paschendale1917/motocounter/photo_2025-11-30_00-51-59.jpg

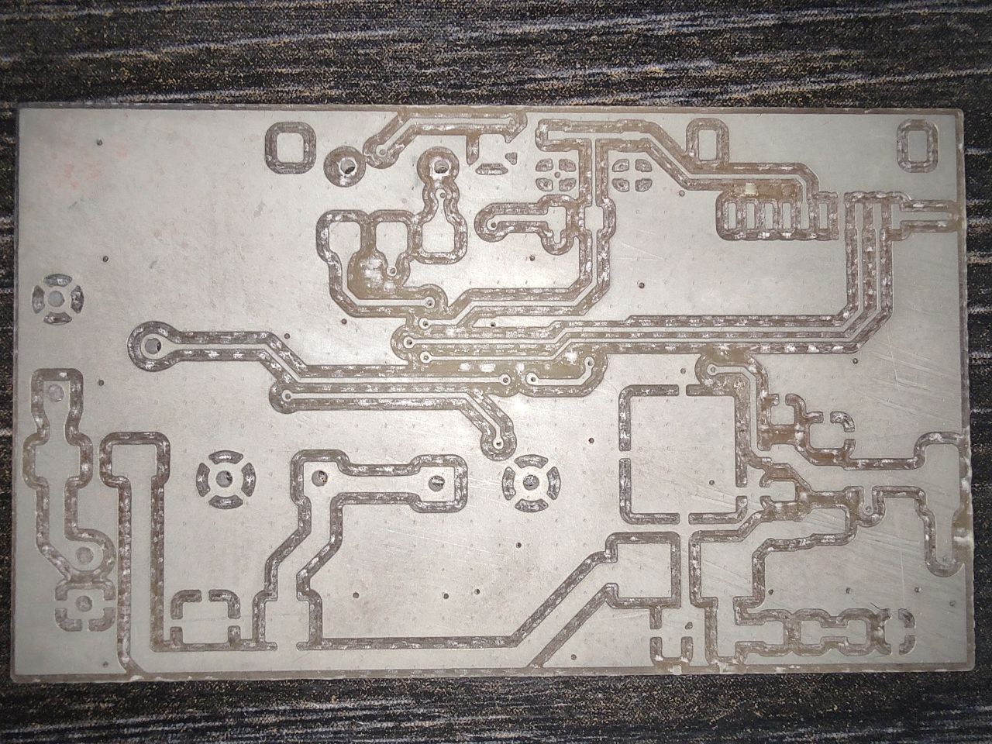
photo_2025-11-30_00-51-59.jpg
