paschendale1917/motocounter/motocounter_keil_project/user_drivers/ws2812/ws2812_dma.c

//ЩАДЯЩИЙ ОПЕРАТИВКУ МЕТОД.ПРИНЦИП РАБОТЫ. 
//создаем два массива: pwm_array для для значений скажности шим, rgb_buffer для хранения значений цвета из расчета 3 байта(r,g,b) на 1 светодиод(у меня 320 светодиодов *3=960 байт)
//настраиваем любой канал любого таймера на частоту 800 кГц(описание как это сделать для светодиодов 2812 в заголовочном файле) и на вызов дма при совпадении 
//настраиваем дма в кольцевом режиме, включаем перерывания по передаче половины данных и по окончанию передачи, при этом работа идет с pwm_array и размером для передачи будет 48 байт(8 бит на цвет*3 цвета=24 бита; 24*2=48 бит. каждый бит цвета преобразуем в байт скважности)
//первично заполняем массив pwm_array значениями, используя значения из rgb_buffer для двух первых диодов.
//включаем передачу по дма, включаем счет в таймере. далее передается "верхняя" половины буфера pwm_array(первый светодиод), затем происходит прерывание HT, в нем происходит заполнение уже переданной "верхней" части массива pwm_array
//далее выход из прерывания, передача "нижней" половины массива pwm_array, вновь вход в прерывание, но уже по окончанию передачи(TC) и в этом прерывания происходит обновление "нижней" части массива
//так как дма  в кольцевом режиме, то вновь начинается передача "верхней" половины pwm_array, а там уже лежат значения скважности уже для третьего диода, затем нижней, где данные 4 светика и так далее
//передача будет длиться, пока ее насильно не отключим
//мы это делаем после того, как закончатся светодиоды в нашей матрице(320 штук)
//после передачи скважностей для всех светодиодов требуется послать сигнал ресет для светодиодов-их протокол требует после послыки данных для n светодиодов прижать линию к земле на время >50 мкс. 
//для этого мы шлем данные для двух светодиодов со скважностью шим == 0(но не нулю для диодов 2812, где скважность =1/3 от полного периода)
//два дня сидел, чтобы нарезать дупля в этой бодяге и суметь ее реализовать максимально понятным для нуба образом
//setcolor(ORANGE_LED);
//send_data();
//https://www.thevfdcollective.com/blog/stm32-and-sk6812-rgbw-led

//ОПЕРАТИВОЗАТРАТНЫЙ МЕТОД(g030 не вывозит 320 диодов с использованием этого метода,f103  с его 20 кб оперативки запросто вывезет)
//пример подготовки буфера для NUM_LEDS светодиодов		
//	ws2812_setcolor(NUM_LEDS, GREEN_LED);
//	ws2812_send();
//в данном примере не используются прерывания таймера для формирования задержки.
//задержка добавляется в конец буфера с данными
// ДМА настраивается на прерывания по окончанию передачи(КОЛЬЦЕВОЙ РЕЖИМ ОТКЛЮЧЕН)
//таймер настраивается ШИМ с частотой 800 кГц
//запускается ДМА, буфер отправляется в CCR, после передачи данных возникает прерывание, где очищаются флаги прерываний и выключается счет в таймере

#include "ws2812_dma.h"

//uint8_t  color_array[DATA_LENTH]={0,};
volatile uint32_t num_bytes=NUM_BYTES;
uint8_t bus_ready=0;
uint8_t rgb_buffer[NUM_BYTES]={0,};
uint8_t pwm_array[2*3*8]={0,}; //буфер для 2х диодов по 24 бита на диод
uint8_t ht_flag=0;
uint8_t ct_flag=0;
static uint32_t px=3;

const uint8_t gammaTable[] = {
    0, 0,  0,  0,  0,  0,  0,  0,  0,  0,  0,  0,  0,  0,  0,  0,
    0,  0,  0,  0,  0,  0,  0,  0,  0,  0,  0,  0,  1,  1,  1,  1,
    1,  1,  1,  1,  1,  1,  1,  1,  1,  2,  2,  2,  2,  2,  2,  2,
    2,  3,  3,  3,  3,  3,  3,  3,  4,  4,  4,  4,  4,  5,  5,  5,
    5,  6,  6,  6,  6,  7,  7,  7,  7,  8,  8,  8,  9,  9,  9, 10,
   10, 10, 11, 11, 11, 12, 12, 13, 13, 13, 14, 14, 15, 15, 16, 16,
   17, 17, 18, 18, 19, 19, 20, 20, 21, 21, 22, 22, 23, 24, 24, 25,
   25, 26, 27, 27, 28, 29, 29, 30, 31, 32, 32, 33, 34, 35, 35, 36,
   37, 38, 39, 39, 40, 41, 42, 43, 44, 45, 46, 47, 48, 49, 50, 50,
   51, 52, 54, 55, 56, 57, 58, 59, 60, 61, 62, 63, 64, 66, 67, 68,
   69, 70, 72, 73, 74, 75, 77, 78, 79, 81, 82, 83, 85, 86, 87, 89,
   90, 92, 93, 95, 96, 98, 99,101,102,104,105,107,109,110,112,114,
  115,117,119,120,122,124,126,127,129,131,133,135,137,138,140,142,
  144,146,148,150,152,154,156,158,160,162,164,167,169,171,173,175,
  177,180,182,184,186,189,191,193,196,198,200,203,205,208,210,213,
  215,218,220,223,225,228,231,233,236,239,241,244,247,249,252,255 };


void init_gpio_ws2812(void){
	//TIM3 CH2
	
	SET_BIT(RCC->IOPENR,RCC_IOPENR_GPIOAEN);
	MODIFY_REG(GPIOA->MODER,GPIO_MODER_MODE7,0x02<<GPIO_MODER_MODE7_Pos); //альтернативная функция вывода
	CLEAR_BIT(GPIOA->OTYPER,GPIO_OTYPER_OT7);//push-pull
	CLEAR_BIT(GPIOA->PUPDR,GPIO_PUPDR_PUPD7);//No pull-up, pull-down
	MODIFY_REG(GPIOA->OSPEEDR,GPIO_OSPEEDR_OSPEED7,0x03<<GPIO_OSPEEDR_OSPEED7_Pos);
	SET_BIT(GPIOA->AFR[0],GPIO_AFRL_AFSEL7_0);	//AFR[0]==AFRL; AFR[1]==AFRH;AFSEL7_0 -нога PA7, альтенативная функция AF1, нулевой бит в AFSEL устанавливаем в единицу
}


void init_ws2812(void){
	
	init_gpio_ws2812();
	SET_BIT(RCC->AHBENR,RCC_AHBENR_DMA1EN);
	SET_BIT(RCC->APBENR1,RCC_APBENR1_TIM3EN);
	
	//настройка таймера
	//SET_BIT(TIM3->CR1,TIM_CR1_ARPE);																									// режим предзагрузки для регистра ARR
	CLEAR_BIT(TIM3->CR1,TIM_CR1_CMS);																									//счет либо от нуля, либо от значения ARR
	CLEAR_BIT(TIM3->CR1,TIM_CR1_DIR);																									//счет вверх
	MODIFY_REG(TIM3->CCMR1,TIM_CCMR1_OC2M,0x06<<TIM_CCMR1_OC2M_Pos);									//шим mode 1 на 2  канале таймера
	SET_BIT(TIM3->CCMR1,TIM_CCMR1_OC2PE);																							//буферизация регистра CCR1:новое значение из буфера передаётся  при каждом событии обновления
	SET_BIT(TIM3->CCER,TIM_CCER_CC2E);																								//разрешаем таймеру использовать ножку микроконтроллера

	//настройка DMA
	
	
	 DMA1_Channel1->CPAR = (uint32_t)(&TIM3->CCR2); 												 //куда пишем
	 DMA1_Channel1->CMAR = (uint32_t)pwm_array; 														 //откуда берем данные для передачи
	 DMA1_Channel1->CNDTR = 48;															 								 //устанoвка количества передаваемых данных	
  
	SET_BIT(DMA1_Channel1->CCR,DMA_CCR_DIR);  															 //1 - из памяти в периферию
	SET_BIT(DMA1_Channel1->CCR,DMA_CCR_TCIE); 															 // прерывание дма по окончанию передачи данных
	SET_BIT(DMA1_Channel1->CCR,DMA_CCR_HTIE); 															 // прерывание дма по передаче половины данных
	CLEAR_BIT(DMA1_Channel1->CCR,DMA_CCR_MEM2MEM| DMA_CCR_PINC);						 //режим MEM2MEM отключен\инкремент адреса периферии отключен
	SET_BIT(DMA1_Channel1->CCR,DMA_CCR_MINC); 															 //Включить инкремент адреса памяти
	SET_BIT(DMA1_Channel1->CCR,DMA_CCR_CIRC); 															 //кольцевой режим
	MODIFY_REG(DMA1_Channel1->CCR,DMA_CCR_PL, 	 0x01 << DMA_CCR_PL_Pos); 			 //приоритет низкий
	MODIFY_REG(DMA1_Channel1->CCR,DMA_CCR_MSIZE, 0x00 << DMA_CCR_MSIZE_Pos); //разрядность данных в памяти 8 бит
	MODIFY_REG(DMA1_Channel1->CCR,DMA_CCR_PSIZE, 0x01 << DMA_CCR_PSIZE_Pos); //разрядность регистра данных 16 бит 
	DMAMUX1_Channel0->CCR=(33 << DMAMUX_CxCR_DMAREQ_ID_Pos); 								 //выбираем вход мультиплексора DMA для канала 2 таймера TIM3(по таблице в разделе DMAmux)
	SET_BIT(TIM3->DIER,TIM_DIER_CC2DE);																			 //разрешение запроса DMA в случае  срабатывания схемы сравнения  канала 2
	NVIC_EnableIRQ(DMA1_Channel1_IRQn);

}

void reset_pwmbuffer(void){
	for (uint8_t i=0;i<48;i++){
		pwm_array[i] = 0;
	}
}

void reset_rgbbuffer(void){
	for (uint8_t i=0;i<48;i++){
		rgb_buffer[i] = 0;
	}
}


void bus_reset(void){
	bus_ready=0;
	reset_pwmbuffer();
	CLEAR_BIT(DMA1_Channel1->CCR,DMA_CCR_EN);																	 //выключение каналa ДМА 																															 //после пересылки всех данных, включая ресет, устанавливаем флаг занятости шины в ноль. в этом случае становится возможным первичное наполнение буфера pwm_array	
	CLEAR_BIT(TIM3->CR1,TIM_CR1_CEN);                                          //останов счета в таймере
}


void send_data_leds(void){
	if(!bus_ready){																															 //если шина не занята
		bus_ready=1;                                                               //устанавливаем флаг занятости шины 
		reset_pwmbuffer();
																	  //включение каналa ДМА для отправки заполненного буфера ШИМ
  
	}

	for (uint8_t i=0;i<8;i++){
		pwm_array[i] 	= (((rgb_buffer[0] << i) & 0x80)) ? WS2812_1 : WS2812_0; //первоначальное заполнение буфера ШИМ
		pwm_array[i+8] 	= (((rgb_buffer[1] << i) & 0x80)) ? WS2812_1 : WS2812_0;
		pwm_array[i+16] = (((rgb_buffer[2] << i) & 0x80)) ? WS2812_1 : WS2812_0;
		pwm_array[i+24] = (((rgb_buffer[3] << i) & 0x80)) ? WS2812_1 : WS2812_0;
		pwm_array[i+32] = (((rgb_buffer[4] << i) & 0x80)) ? WS2812_1 : WS2812_0;
		pwm_array[i+40] = (((rgb_buffer[5] << i) & 0x80)) ? WS2812_1 : WS2812_0;
	}
		
   DMA1->IFCR=1;                                    												  //очищаем  флаги прерываний DMA
   DMA1_Channel1->CNDTR = 48;                                                 //устанoвка количества передаваемых данных
   WRITE_REG(TIM3->ARR,BIT_TIME);                                             //установка частоты ШИМ
   WRITE_REG(TIM3->CNT,0);                                                    //очистка счетного регистра 
   WRITE_REG(TIM3->CCR2,0);                                                   //устанавка скважностм ШИМ 0, чтобы ножка была в неактивном состоянии(не дергалась)
   SET_BIT(TIM3->CR1,TIM_CR1_CEN);                                            //запуск счета в таймере
   SET_BIT(DMA1_Channel1->CCR,DMA_CCR_EN);	
}


void DMA1_Channel1_IRQHandler(void){

	 
	if(HALF_TRANSFER_COMPLETE_WS2812){	
		for (uint8_t i=0;i<8;i++){
			pwm_array[i] 	= (((rgb_buffer[px] << i) & 0x80)) ? WS2812_1 : WS2812_0;
			pwm_array[i+8] 	= (((rgb_buffer[px+1] << i) & 0x80)) ? WS2812_1 : WS2812_0;
			pwm_array[i+16] = (((rgb_buffer[px+2] << i) & 0x80)) ? WS2812_1 : WS2812_0;
		}
		RESET_HT_FLAG_WS2812;
		}

	if(TOTAL_TRANSFER_COMPLETE_WS2812){	
		for (uint8_t i=0;i<8;i++){
			pwm_array[i+24] = (((rgb_buffer[px] << i) & 0x80)) ? WS2812_1 : WS2812_0;
			pwm_array[i+32] = (((rgb_buffer[px+1] << i) & 0x80)) ? WS2812_1 : WS2812_0;
			pwm_array[i+40] = (((rgb_buffer[px+2] << i) & 0x80)) ? WS2812_1 : WS2812_0;
		}
		RESET_TC_FLAG_WS2812;	

	 }
		px+=3;															//счетчик уже использованных байт в массиве rgb_buffer//для каждого светодиода три байта
		if(px>NUM_BYTES){	                                                       //обязательно сначала нужно проверить, иначе пока выполняется код ниже, таймер настрогает дополнительно пачку битов, которые светодиодом могут интерпертироваться как данные
		bus_reset();
		px=3; 																	//первые три пикселя зажигаем в функции send_data(), поэтому счет начинается с 3//в ней мы заполняем pwm_buffer для первоначальной отправки
	}
		
}

void led_set_RGB(uint16_t index, uint8_t r, uint8_t g, uint8_t b) {
  rgb_buffer[3 * index    ] = g;
  rgb_buffer[3 * index + 1] = r;
  rgb_buffer[3 * index + 2] = b;
 
}

void led_set_all_RGB(uint8_t r, uint8_t g, uint8_t b) {
  for(uint16_t i = 0; i < NUM_LEDS; i++) led_set_RGB(i, r, g, b);
}

void setcolor(uint32_t color){  //HEX
	uint8_t g,r,b;
	r=(uint8_t)(color>>16);
	g=(uint8_t)(color>>8);
	b=(uint8_t)color;
	for(uint16_t i = 0; i < NUM_LEDS; i++) led_set_RGB(i, r, g, b);
	
}

void leds_off(void){
	for(uint16_t i = NUM_LEDS; i >0; i--){
		setcolor(OFF_LED);
		send_data_leds();
		_delay_ms(1);
	}
}


void policecolor_blink(void){
	for(uint8_t k=0;k<6;k++){
		for(uint16_t i = 0; i <NUM_LEDS/2; i++) led_set_RGB(i, 255, 0, 0);
		for(uint16_t i = NUM_LEDS/2; i <NUM_LEDS; i++) led_set_RGB(i, 0, 0, 0);
		send_data_leds();
		_delay_ms(40);
		leds_off();
		_delay_ms(40);
	}

	for(uint8_t k=0;k<6;k++){
		for(uint16_t i = 0; i <NUM_LEDS/2; i++) led_set_RGB(i, 0, 0, 0);
		for(uint16_t i = NUM_LEDS/2; i <NUM_LEDS; i++) led_set_RGB(i, 0, 0, 255);
		send_data_leds();
		_delay_ms(40);
		leds_off();
		_delay_ms(40);
	}

}



void policecolor_breathe(void){  //HEX
	 volatile uint16_t i=0;
	 volatile uint16_t j=0; 
	for(uint8_t g=0;g<255;g++){
		for(  i = 0; i <NUM_LEDS/2; i++) led_set_RGB(i, g, 0, 0);
		for(  j = NUM_LEDS/2; j <NUM_LEDS; j++) led_set_RGB(j, 0, 0, 0);
		send_data_leds();
		_delay_ms(2);
	}
	for(uint8_t g=255;g>0;g--){
		for(uint16_t i = 0; i <NUM_LEDS/2; i++) led_set_RGB(i, g, 0, 0);
		for(uint16_t j = NUM_LEDS/2; j <NUM_LEDS; j++) led_set_RGB(j, 0, 0, 0);
		send_data_leds();
		_delay_ms(2);
	}
	for(uint8_t g=0;g<255;g++){
		for(uint16_t i = 0; i <NUM_LEDS/2; i++) led_set_RGB(i, 0, 0, 0);
		for(uint16_t j = NUM_LEDS/2; j <NUM_LEDS; j++) led_set_RGB(j, 0, 0, g);
		send_data_leds();
		_delay_ms(2);
	}
 for(uint8_t g=255;g>0;g--){
		for(uint16_t i = 0; i <NUM_LEDS/2; i++) led_set_RGB(i, 0, 0, 0);
		for(uint16_t j = NUM_LEDS/2; j <NUM_LEDS; j++) led_set_RGB(j, 0, 0, g);
		send_data_leds();
		_delay_ms(2);
	}
}


void start_effect(void){
	 uint32_t color=PURPLE_LED;
	uint32_t secondcolor=ORANGE_LED;
		for(int16_t i = 0; i <NUM_LEDS; i++){
			led_set_RGB(i, (uint8_t)(color>>8), (uint8_t)(color>>16), (uint8_t)(color));
			send_data_leds();
			_delay_ms(30);
			setcolor(OFF_LED);
			send_data_leds();
			_delay_ms(5);
		}
		for(int16_t i = NUM_LEDS; i >=0; i--){
			led_set_RGB(i, (uint8_t)(secondcolor>>16), (uint8_t)(secondcolor>>8), (uint8_t)(secondcolor));
			send_data_leds();
			_delay_ms(30);
			setcolor(OFF_LED);
			send_data_leds();
			_delay_ms(5);
		}

}
