paschendale1917/motocounter/motocounter_keil_project/user_drivers/st7735/ArialNumFontPlus.c

// SevenSegNumFontPlus.c
// Font type    : Special (SubSet)
// Font size    : 32x50 pixels
// Memory usage : 2204 bytes

#if defined(__AVR__)
	#include <avr/pgmspace.h>
	#define fontdatatype const uint8_t
#elif defined(__PIC32MX__)
	#define PROGMEM
	#define fontdatatype const unsigned char
#elif defined(__arm__)
	#define PROGMEM
	#define fontdatatype const unsigned char
#endif

fontdatatype ArialNumFontPlus[2204] PROGMEM={
0x20,0x32,0x30,0x0B,
0x00,0x00,0x00,0x00,0x00,0x00,0x00,0x00,0x00,0x0F,0xF0,0x00,0x00,0x1F,0xF8,0x00,0x00,0x7F,0xFE,0x00,0x00,0xFF,0xFF,0x00,0x01,0xFF,0xFF,0x00,0x03,0xF8,0x1F,0x80,0x03,0xF0,0x0F,0xC0,0x07,0xE0,0x07,0xC0,0x07,0xC0,0x03,0xE0,0x0F,0xC0,0x03,0xE0,0x0F,0x80,0x01,0xF0,0x0F,0x80,0x01,0xF0,0x1F,0x80,0x01,0xF0,0x1F,0x00,0x00,0xF8,0x1F,0x00,0x00,0xF8,0x1F,0x00,0x00,0xF8,0x1F,0x00,0x00,0xF8,0x3F,0x00,0x00,0xFC,0x3E,0x00,0x00,0x7C,0x3E,0x00,0x00,0x7C,0x3E,0x00,0x00,0x7C,0x3E,0x00,0x00,0x7C,0x3E,0x00,0x00,0x7C,0x3E,0x00,0x00,0x7C,0x3E,0x00,0x00,0x7C,0x3E,0x00,0x00,0x7C,0x3E,0x00,0x00,0x7C,0x3E,0x00,0x00,0x7C,0x3F,0x00,0x00,0x7C,0x1F,0x00,0x00,0xF8,0x1F,0x00,0x00,0xF8,0x1F,0x00,0x00,0xF8,0x1F,0x00,0x00,0xF8,0x0F,0x80,0x01,0xF0,0x0F,0x80,0x01,0xF0,0x0F,0x80,0x01,0xF0,0x07,0xC0,0x03,0xE0,0x07,0xC0,0x03,0xE0,0x03,0xE0,0x07,0xC0,0x03,0xF0,0x0F,0xC0,0x01,0xF8,0x1F,0x80,0x00,0xFF,0xFF,0x00,0x00,0xFF,0xFE,0x00,0x00,0x7F,0xFC,0x00,0x00,0x1F,0xF8,0x00,0x00,0x07,0xE0,0x00,0x00,0x00,0x00,0x00,0x00,0x00,0x00,0x00,  // 0 neu
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
};
