paschendale1917/motocounter/motocounter_keil_project/user_drivers/st7735/GroteskBold16x32_DK_NO.c

// GroteskBold16x32_DK_NO.c
// Font type    : Full (95 characters)
// Font size    : 16x32 pixels
// Memory usage : 6084 bytes

#if defined(__AVR__)
    #include <avr/pgmspace.h>
    #define fontdatatype const uint8_t
#elif defined(__PIC32MX__)
    #define PROGMEM
    #define fontdatatype const unsigned char
#elif defined(__arm__)
    #define PROGMEM
    #define fontdatatype const unsigned char
#endif

fontdatatype GroteskBold16x32_DK_NO[6084] PROGMEM={
0x10,0x20,0x20,0x5F,
0x00,0x00,0x00,0x00,0x00,0x00,0x00,0x00,0x00,0x00,0x00,0x00,0x00,0x00,0x00,0x00,0x00,0x00,0x00,0x00,0x00,0x00,0x00,0x00,0x00,0x00,0x00,0x00,0x00,0x00,0x00,0x00,0x00,0x00,0x00,0x00,0x00,0x00,0x00,0x00,0x00,0x00,0x00,0x00,0x00,0x00,0x00,0x00,0x00,0x00,0x00,0x00,0x00,0x00,0x00,0x00,0x00,0x00,0x00,0x00,0x00,0x00,0x00,0x00,  // <space>
0x00,0x00,0x00,0x00,0x00,0x00,0x03,0xC0,0x03,0xC0,0x03,0xC0,0x03,0xC0,0x03,0xC0,0x03,0xC0,0x03,0xC0,0x03,0xC0,0x03,0xC0,0x03,0xC0,0x03,0xC0,0x03,0xC0,0x03,0xC0,0x03,0xC0,0x01,0x80,0x01,0x80,0x01,0x80,0x00,0x00,0x00,0x00,0x00,0x00,0x03,0xC0,0x03,0xC0,0x03,0xC0,0x03,0xC0,0x03,0xC0,0x00,0x00,0x00,0x00,0x00,0x00,0x00,0x00,  // !
0x00,0x00,0x00,0x00,0x0E,0x1C,0x0E,0x1C,0x1E,0x3C,0x1E,0x38,0x1C,0x78,0x3C,0x78,0x3C,0x78,0x3C,0x78,0x3C,0x78,0x3C,0x78,0x3C,0x78,0x00,0x00,0x00,0x00,0x00,0x00,0x00,0x00,0x00,0x00,0x00,0x00,0x00,0x00,0x00,0x00,0x00,0x00,0x00,0x00,0x00,0x00,0x00,0x00,0x00,0x00,0x00,0x00,0x00,0x00,0x00,0x00,0x00,0x00,0x00,0x00,0x00,0x00,  // "
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
};
