paschendale1917/motocounter/motocounter_keil_project/user_drivers/buttons/buttons.h

#ifndef buttons_H_
#define buttons_H_

#include "stm32g0xx.h"
#include "../wwdg/WWDG.h"
#include "../st7735_backlight/backlight.h"
#include "../standby_led/standby_led.h"
#include "../st7735/st7735.h"
#include "../menu/handlers.h"

#define BUTTON_LEFT_STATE            	READ_BIT(GPIOC->IDR,GPIO_IDR_ID15)
#define BUTTON_RIGHT_STATE              READ_BIT(GPIOB->IDR,GPIO_IDR_ID7)
#define BUTTON_OK_STATE              	READ_BIT(GPIOB->IDR,GPIO_IDR_ID6)


extern  uint8_t  shortpress_left,
				 shortpress_right,
				 shortpress_ok,
				 longpress_left,
				 longpress_right,
				 longpress_ok;	

typedef struct  {
	uint8_t sec;
	uint8_t min;
	uint16_t hour;
}timer;

extern  timer tim;


#define F_TIM1									64000000
#define F_TIM1_PRESCALED                     	10000												//делитель /частота 64000000:(6399+1)=10000 тиков в секунду - частота, на которой будет работать таймер
#define TIM1_AUTORELOAD                   		100  											   	//значение, до которoго будет считать счетчик;здесь 10000/100=100 прерываний в секунду

#define TIM_EnableCounter(TIMx)    			 	TIMx->CR1 |= TIM_CR1_CEN   							//макрос включения таймера
#define TIM_EnableInterruptUpdate(TIMx) 		TIMx->DIER |= TIM_DIER_UIE 							// макрос разрешения обновления прерываний

#define SHORT_TIMEOUT 39
#define LONG_TIMEOUT  40

//настройки для меню

#define PRESSED 	1    
#define UNPRESSED 0

#define NUM_BUTTONS 6     //количество кнопок      

typedef  enum{
  BUTTON_LEFT    		=  0 ,
  BUTTON_RESET    		=  1 ,
  BUTTON_MENUITEMBACK   =  2 ,
  BUTTON_RIGHT   	 	=  3 ,
  BUTTON_SELECT   		=  4 ,
  BUTTON_ENTERMENU 		=  5 ,
  BUTTON_NOTHING  		=  255 
} Button_TypeDef;


void buttons_init(void);
uint8_t readButtonState(void);
void resetButton(void);
void _delay_ms_tim1(uint16_t ms);

#endif /* buttons_H__ */
