paschendale1917/motocounter/motocounter_keil_project/user_drivers/RCC/RCC.c

#include "RCC.h"

void set_sysclk64(void){
	RCC->PLLCFGR|=RCC_PLLCFGR_PLLSRC_HSI; 									//тактирование от HSI16
	
	FLASH->ACR&=~FLASH_ACR_PRFTEN; 											//настройка флэш
	FLASH->ACR|=FLASH_ACR_PRFTEN;
	FLASH->ACR|=FLASH_ACR_LATENCY_2; 
	
	RCC->PLLCFGR&=~RCC_PLLCFGR_PLLM_Msk;									//M==1 делитель выхода PLL(HSI16/1=16)
	
	RCC->PLLCFGR&=~RCC_PLLCFGR_PLLN_Msk;									//очистка на всякий случай
	RCC->PLLCFGR|=RCC_PLLCFGR_PLLN_3;										//N==8 множитель(PLLvco=16*8=128)
	
	RCC->PLLCFGR|=RCC_PLLCFGR_PLLR_0;  										//R==2 делитель PLLCLK=SYSCLK=128/2=64 MHz //установка частоты SYSCLK
	
	RCC->CFGR|=(1<<RCC_CFGR_HPRE_Pos);										//AHB prescaler 1 //шина AHB=SYSCLK/1=64MHz
	
	MODIFY_REG(RCC->CFGR,RCC_CFGR_PPRE,0x00<<RCC_CFGR_PPRE_Pos);			//APB prescaler 4;APB = 64/4=16 MHz //таймеры TIM16 и TIM17 64 MHz  в ранних ревизиях чипа. смотреть errata
	
	//делитель для настройки частоты работы ADC
	RCC->PLLCFGR&=~RCC_PLLCFGR_PLLP_Msk;									//очистка на всякий случай
	RCC->PLLCFGR|=RCC_PLLCFGR_PLLP_2;										//P==4 // тактирование  adc 64/4=16 MHz
	RCC->PLLCFGR|=RCC_PLLCFGR_PLLPEN;										//PLLPCLK clock output enable
	
	

	RCC->CR |=RCC_CR_PLLON; 												//запускаем pll
	while(RCC->CR & (RCC_CR_PLLRDY));
	RCC->PLLCFGR |= RCC_PLLCFGR_PLLREN;
	RCC->CFGR|=RCC_CFGR_SW_1;												//тактирование от PLLRCLK 64 MHz
	
}
